PrinceOfPuppers/atmega16u2-crt/schematic/schematic.kicad_sch

## KiCad design schematic/schematic.kicad_sch (2024-05-28)

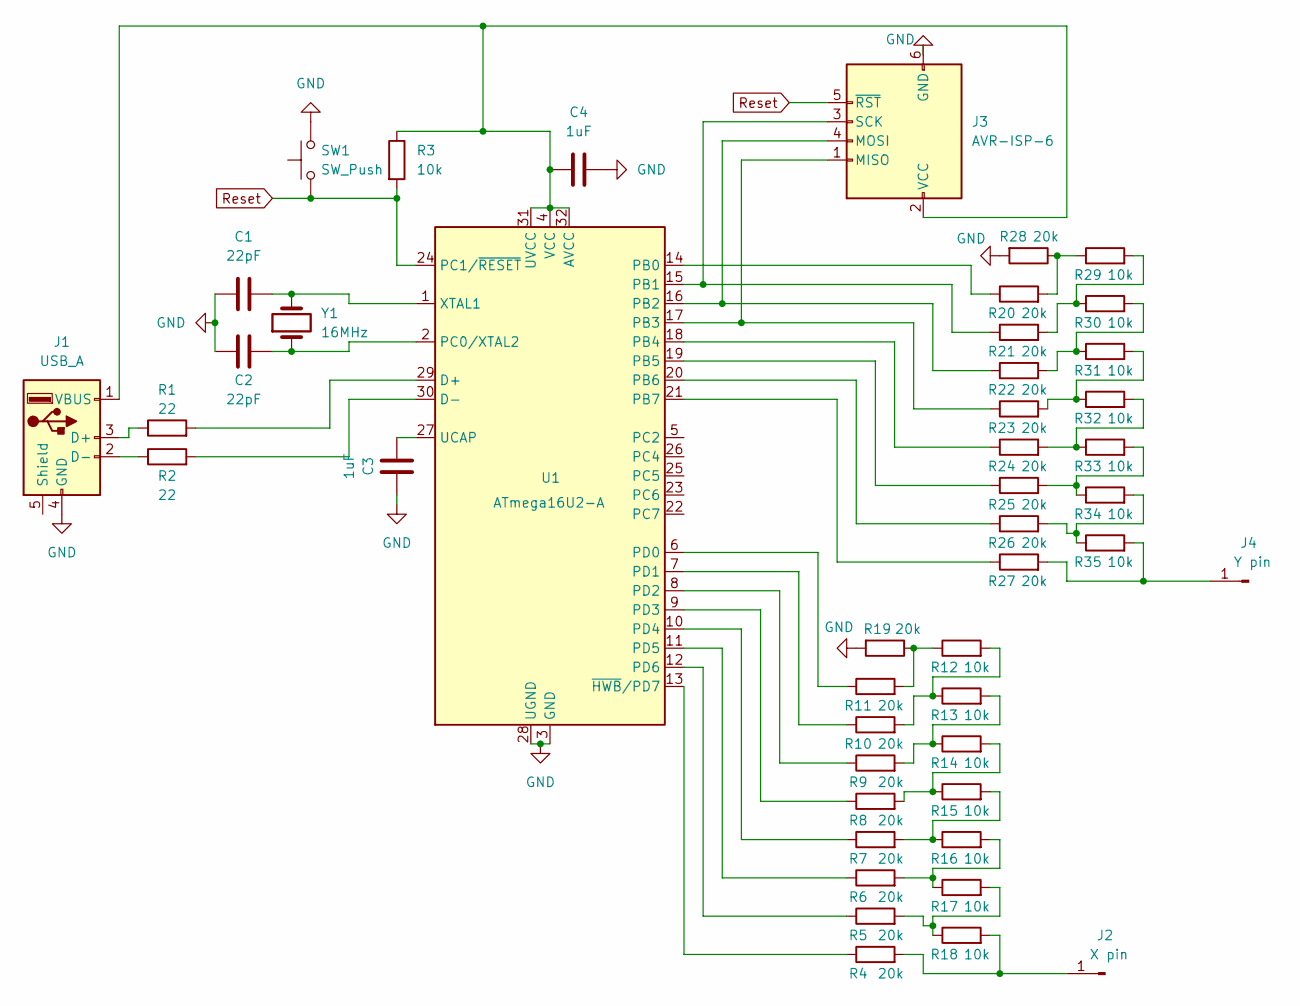
[picture p5: schematic schematic.kicad_sch]

Parts:
C1, C2: 22pF; C_0603_1608Metric
C3, C4: 1uF; C_0603_1608Metric
J1: USB_A; USB_A_CNCTech_1001-011-01101_Horizontal
J2: X pin; PinHeader_1x01_P2.54mm_Horizontal
J3: AVR-ISP-6; PinHeader_2x03_P2.54mm_Horizontal
J4: Y pin; PinHeader_1x01_P2.54mm_Horizontal
R1, R2: 22; R_0603_1608Metric
R3, R12, R13, R14, R15, R16, R17, R18, R29, R30, R31, R32, R33, R34, R35: 10k; R_0603_1608Metric
R4, R5, R6, R7, R8, R9, R10, R11, R19, R20, R21, R22, R23, R24, R25, R26, R27, R28: 20k; R_0603_1608Metric
SW1: SW_Push; SW_Tactile_SPST_NO_Straight_CK_PTS636Sx25SMTRLFS
U1: ATmega16U2-A; TQFP-32_7x7mm_P0.8mm
Y1: 16MHz; Crystal_HC49-4H_Vertical

Connections:
GND: C1.1, C2.1, C3.2, C4.2, J1.4 (GND), J3.6 (GND), R19.2, R28.2, SW1.2, U1.3 (GND), U1.28 (UGND)
unnamed: C1.2, U1.1 (XTAL1), Y1.2
unnamed: C2.2, U1.2 (PC0/XTAL2), Y1.1
unnamed: C3.1, U1.27 (UCAP)
unnamed: C4.1, J1.1 (VBUS), J3.2 (VCC), R3.1, U1.4 (VCC), U1.31 (UVCC), U1.32 (AVCC)
unnamed: J1.2 (D-), R2.1
unnamed: J1.3 (D+), R1.1
unnamed: J2.1, R4.2, R18.2
unnamed: J3.1 (MISO), R23.1, U1.17 (PB3)
unnamed: J3.3 (SCK), R21.1, U1.15 (PB1)
unnamed: J3.4 (MOSI), R22.1, U1.16 (PB2)
unnamed: J4.1, R27.2, R35.2
unnamed: R1.2, U1.29 (D+)
unnamed: R2.2, U1.30 (D-)
unnamed: R4.1, U1.13 (~HWB/PD7)
unnamed: R5.1, U1.12 (PD6)
unnamed: R6.1, U1.11 (PD5)
unnamed: R7.1, U1.10 (PD4)
unnamed: R8.1, U1.9 (PD3)
unnamed: R9.1, U1.8 (PD2)
unnamed: R10.1, U1.7 (PD1)
unnamed: R10.2, R12.2, R13.1
unnamed: R11.1, U1.6 (PD0)
unnamed: R11.2, R12.1, R19.1
unnamed: R9.2, R13.2, R14.1
unnamed: R8.2, R14.2, R15.1
unnamed: R7.2, R15.2, R16.1
unnamed: R6.2, R16.2, R17.1
unnamed: R5.2, R17.2, R18.1
unnamed: R20.1, U1.14 (PB0)
unnamed: R20.2, R28.1, R29.1
unnamed: R21.2, R29.2, R30.1
unnamed: R22.2, R30.2, R31.1
unnamed: R23.2, R31.2, R32.1
unnamed: R24.1, U1.18 (PB4)
unnamed: R24.2, R32.2, R33.1
unnamed: R25.1, U1.19 (PB5)
unnamed: R25.2, R33.2, R34.1
unnamed: R26.1, U1.20 (PB6)
unnamed: R26.2, R34.2, R35.1
unnamed: R27.1, U1.21 (PB7)
Reset: J3.5 (~RST), R3.2, SW1.1, U1.24 (PC1/~RESET)
